LukeCepza/SomaStim/Others/Matlab/Sos2.png

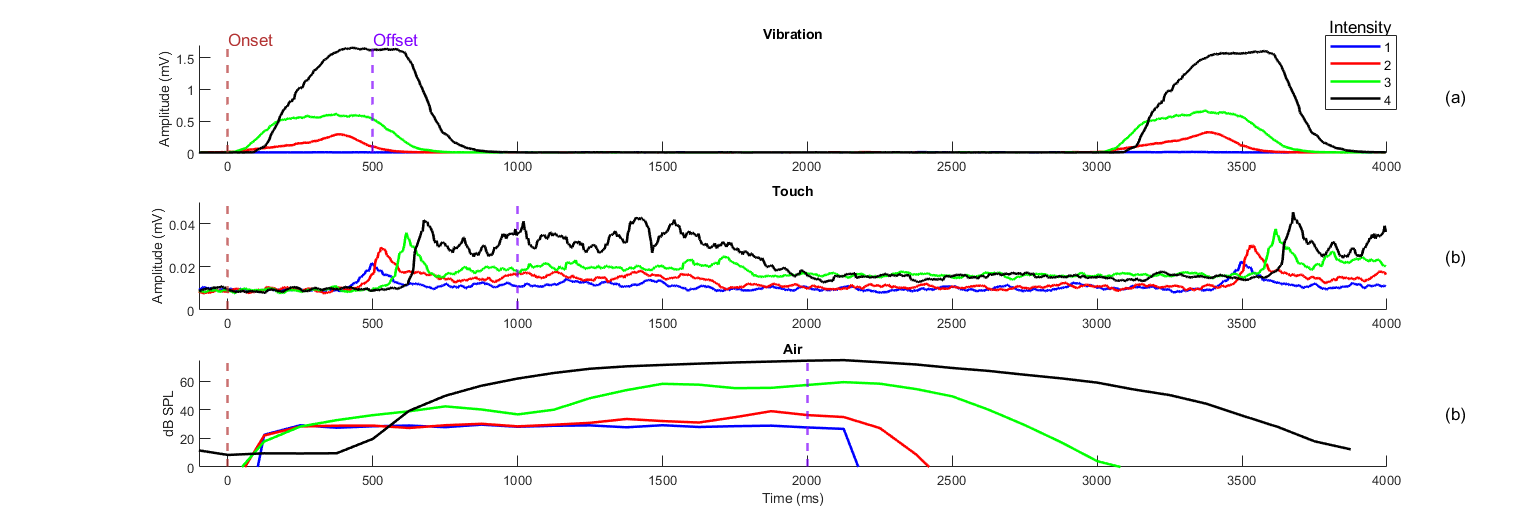
Others/Matlab/Sos2.png
