LukeCepza/SomaStim/Design/CaressModule_NeuroSense_SLDPRT_STL/CaricasFull - T_MD_LoadCell-1.STL

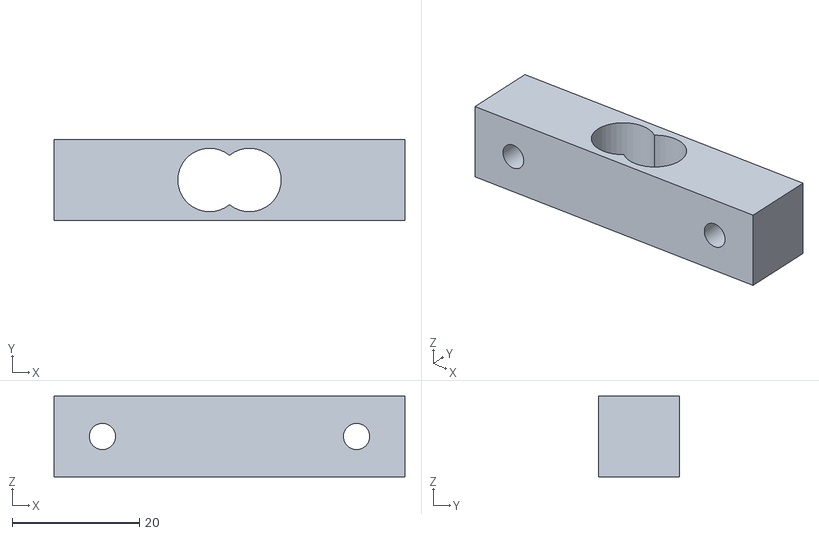
[picture p16: CAD file, 2023-08-07]
Design/CaressModule_NeuroSense_SLDPRT_STL/CaricasFull - T_MD_LoadCell-1.STL
55.2 x 12.7 x 12.7
