LukeCepza/SomaStim/Design/CaressModule_NeuroSense_SLDPRT_STL/CaricasFull - T_MD_RollerAxis-1.STL

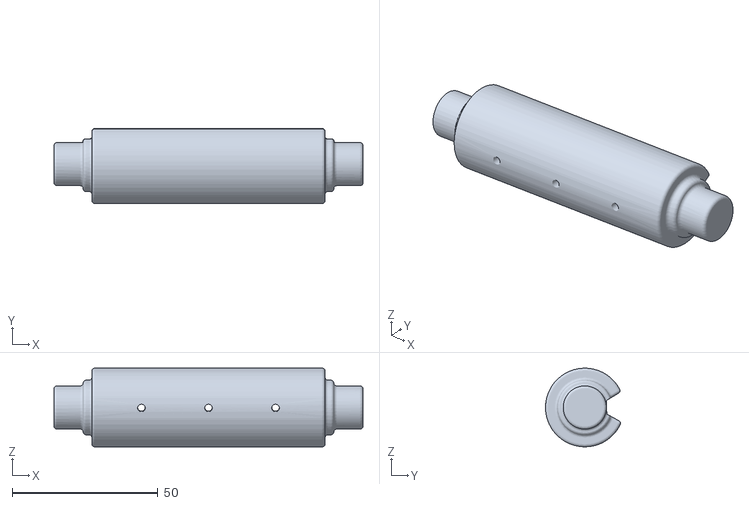
[picture p17: CAD file, 2023-08-07]
Design/CaressModule_NeuroSense_SLDPRT_STL/CaricasFull - T_MD_RollerAxis-1.STL
106.0 x 25.7 x 27.0
