LukeCepza/SomaStim/Design/CaressModule_NeuroSense_SLDPRT_STL/CaricasFull - T_MD_MotorSupport-1.STL

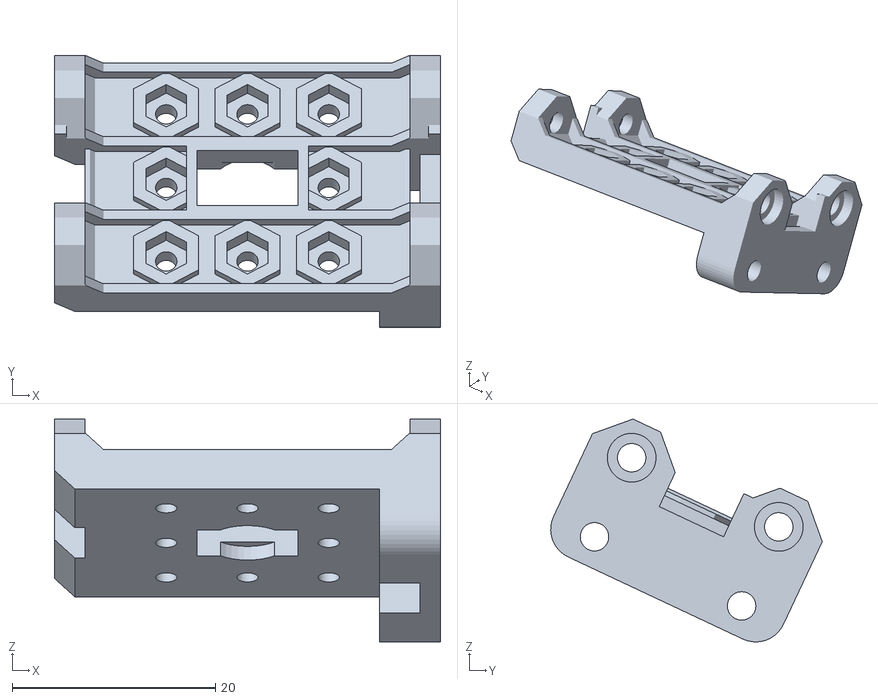
[picture p18: CAD file, 2023-08-07]
Design/CaressModule_NeuroSense_SLDPRT_STL/CaricasFull - T_MD_MotorSupport-1.STL
38.0 x 26.7 x 21.9
