LukeCepza/SomaStim/Design/CaressModule_NeuroSense_SLDPRT_STL/CaricasFull - T_MD_LateralBehind-1.STL

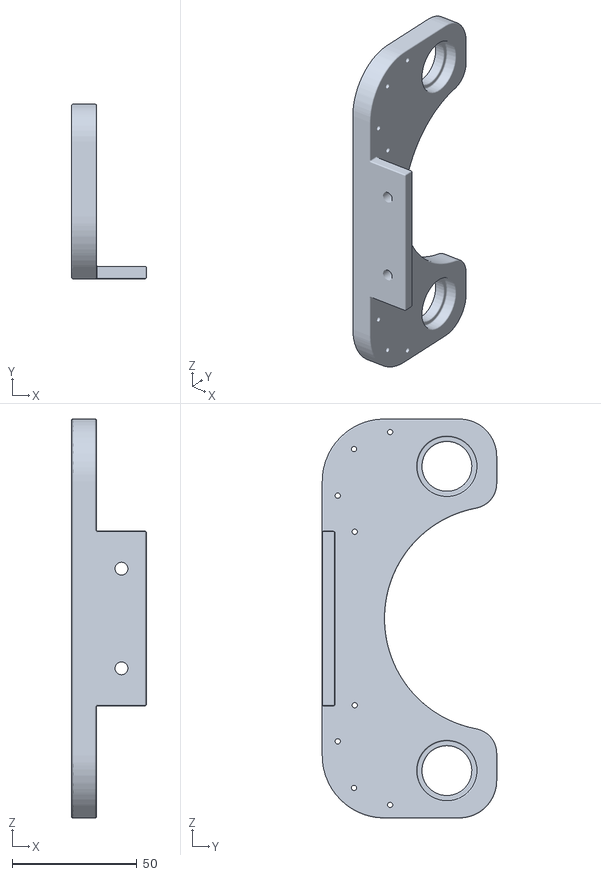
[picture p19: CAD file, 2023-08-07]
Design/CaressModule_NeuroSense_SLDPRT_STL/CaricasFull - T_MD_LateralBehind-1.STL
30.0 x 70.0 x 160.0
