LukeCepza/SomaStim/Design/CaressModule_NeuroSense_SLDPRT_STL/CaricasFull.SLDASM

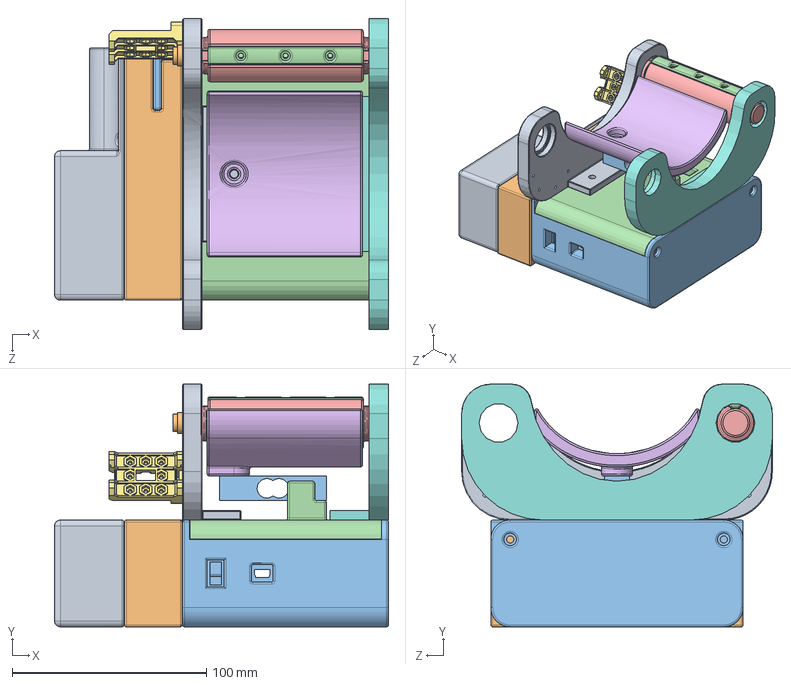
[picture p20: CAD file, 2023-08-07]
Design/CaressModule_NeuroSense_SLDPRT_STL/CaricasFull.SLDASM
172.0 x 125.0 x 160.0 mm
T_MD_CouplingMotor
T_MD_LateralBehind
T_MD_LateralFront
T_MD_LoadCell
T_MD_MotorSupport
T_MD_Plate
T_MD_RollerAxis
T_MD_RollerBar
T_MD_LoadCellBase
T_MD_BaseElectroV2
T_MD_BatteryPack
T_MD_BatteryPackLid
T_MD_18650
