LukeCepza/SomaStim/Design/CaressModule_NeuroSense_SLDPRT_STL/CaricasFull - T_MD_LoadCellBase-1.STL

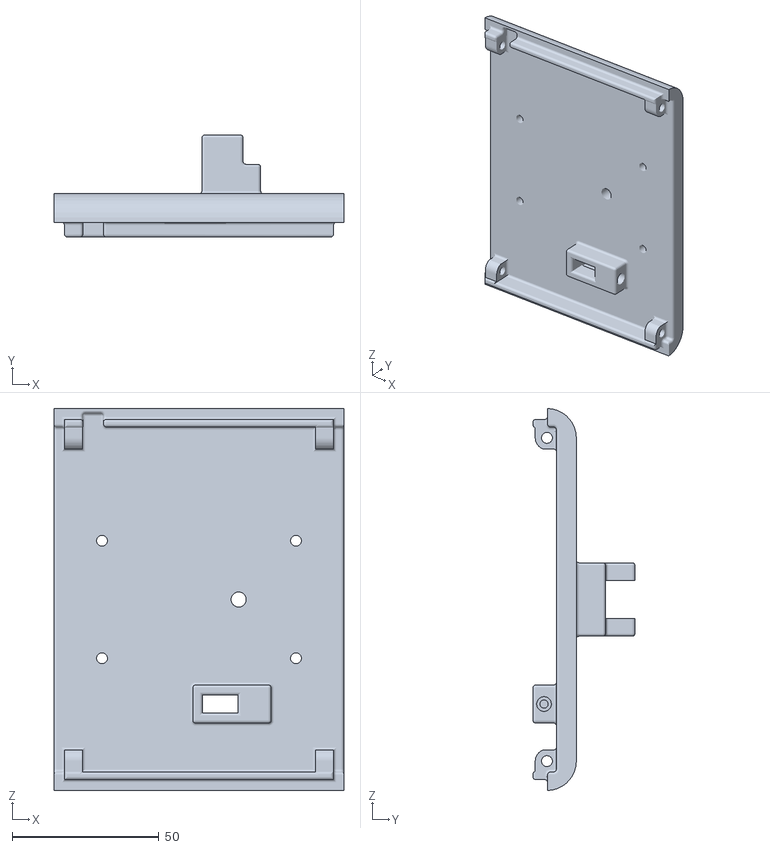
[picture p21: CAD file, 2023-08-07]
Design/CaressModule_NeuroSense_SLDPRT_STL/CaricasFull - T_MD_LoadCellBase-1.STL
98.6 x 34.8 x 130.0
