LukeCepza/SomaStim/Design/CaressModule_NeuroSense_SLDPRT_STL/CaricasFull - T_MD_BatteryPack-1.STL

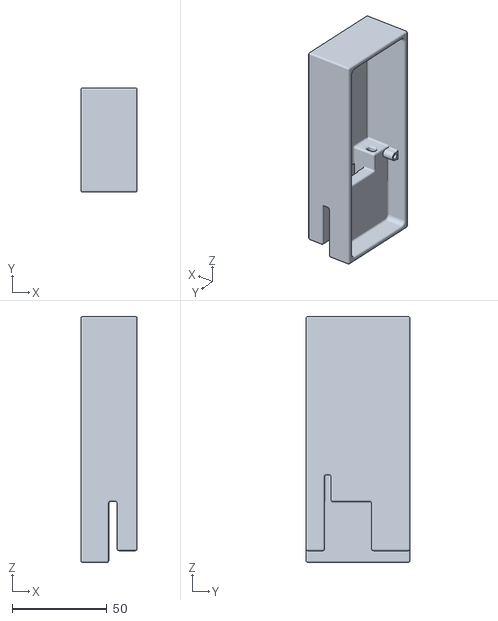
[picture p23: CAD file, 2023-08-07]
Design/CaressModule_NeuroSense_SLDPRT_STL/CaricasFull - T_MD_BatteryPack-1.STL
29.8 x 55.0 x 130.0
