LukeCepza/SomaStim/Design/MasterBox/files/lcd1602_box_and_stand.stl

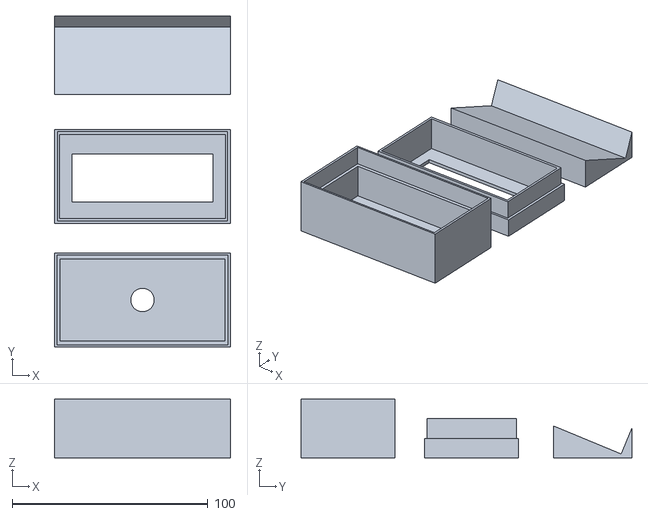
[picture p27: CAD file, 2023-08-01]
Design/MasterBox/files/lcd1602_box_and_stand.stl
90.0 x 169.0 x 30.0
