LukeCepza/SomaStim/Design/MasterBox/MasterBox1_base.STL

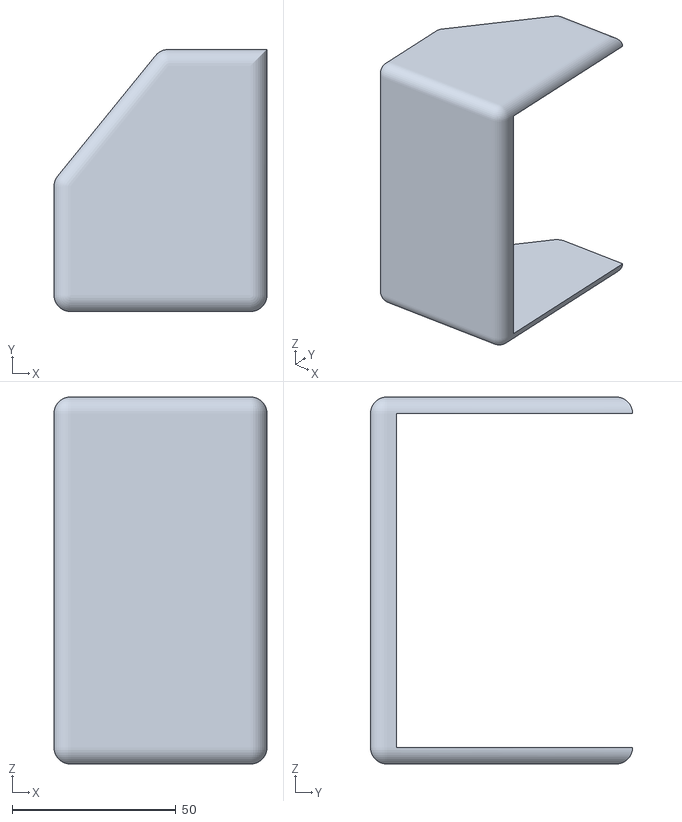
[picture p28: CAD file, 2023-08-01]
Design/MasterBox/MasterBox1_base.STL
65.0 x 80.0 x 112.0
