LukeCepza/SomaStim/Design/VibrationModule/VibrationDownwards_NeuroSense_SLDPRT_STL/V_Base.SLDPRT

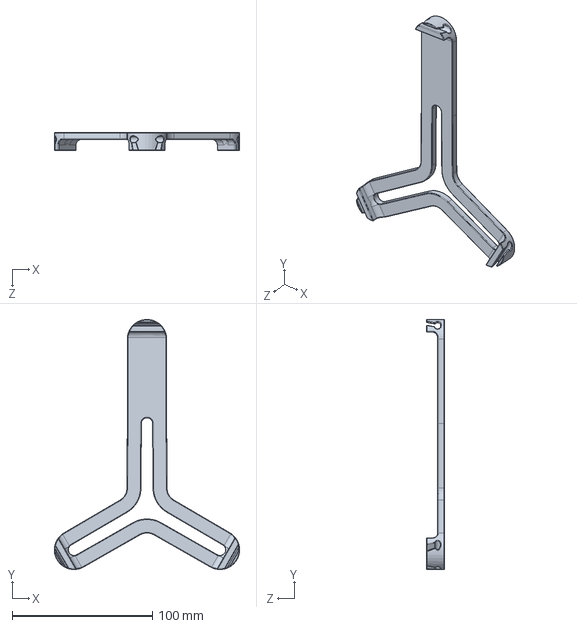
[picture p29: CAD file, 2023-08-01]
Design/VibrationModule/VibrationDownwards_NeuroSense_SLDPRT_STL/V_Base.SLDPRT
131.9 x 178.0 x 13.0 mm
