LukeCepza/SomaStim/PCB/Others/SEN-13879.step

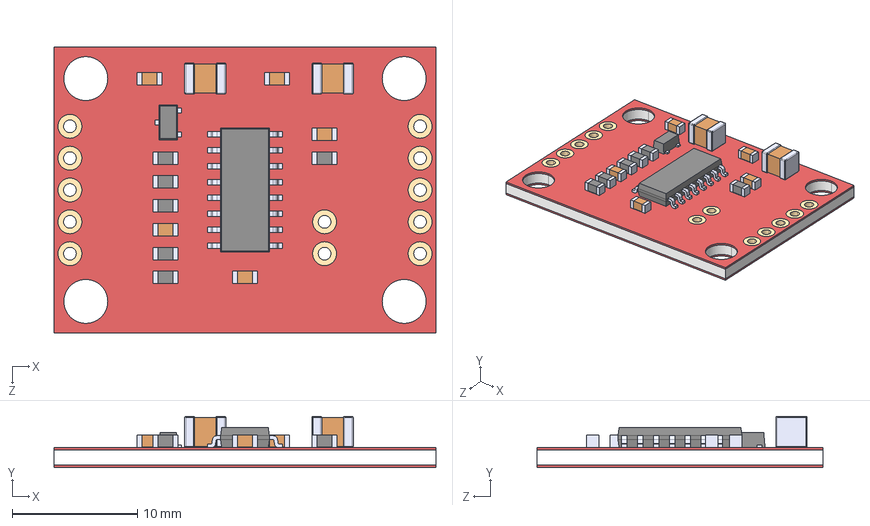
[picture p30: CAD file, 2023-08-07]
PCB/Others/SEN-13879.step
30.5 x 4.10 x 22.9 mm
