LukeCepza/SomaStim/Design/MasterBox/MasterBox1_LadoArduino.STL

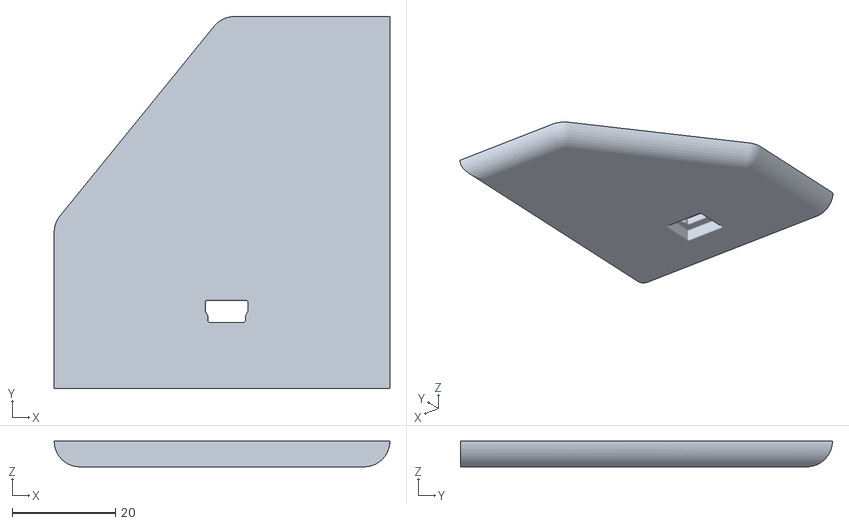
[picture p31: CAD file, 2023-08-01]
Design/MasterBox/MasterBox1_LadoArduino.STL
65.0 x 72.0 x 5.00
