LukeCepza/SomaStim/Design/VibrationModule/VibrationDownwards_NeuroSense_SLDPRT_STL/V_BaseSupport.SLDPRT

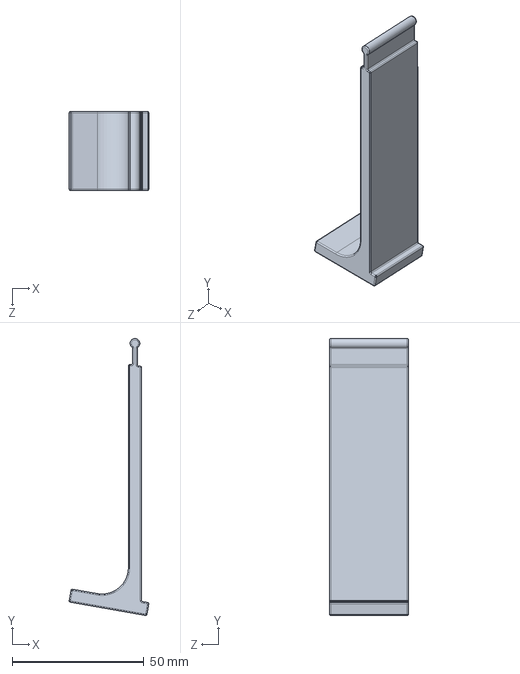
[picture p32: CAD file, 2023-08-01]
Design/VibrationModule/VibrationDownwards_NeuroSense_SLDPRT_STL/V_BaseSupport.SLDPRT
30.3 x 105.1 x 30.0 mm
