LukeCepza/SomaStim/Design/MasterBox/MasterBox1_base2.STL

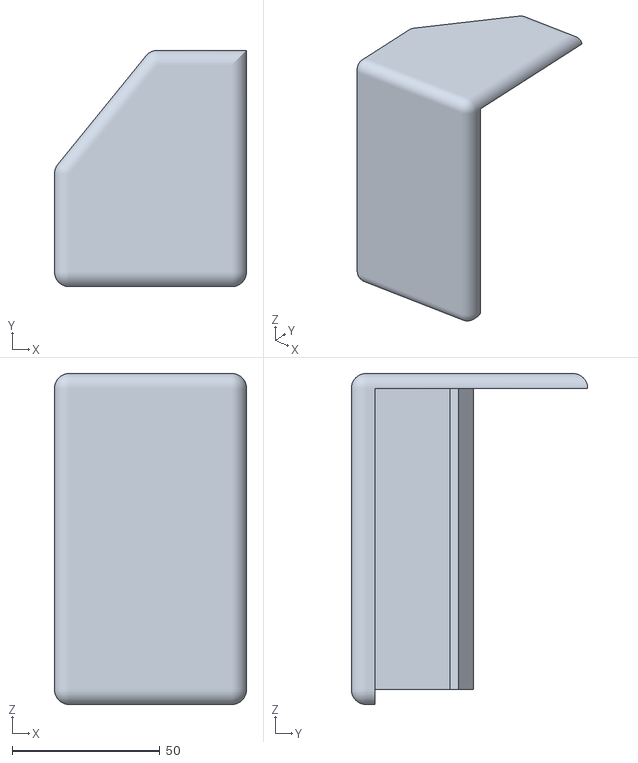
[picture p33: CAD file, 2023-08-01]
Design/MasterBox/MasterBox1_base2.STL
65.0 x 80.0 x 112.0
