LukeCepza/SomaStim/Design/VibrationModule/VibrationDownwards_NeuroSense_SLDPRT_STL/VibrationModule - V_BaseSupport-2.STL

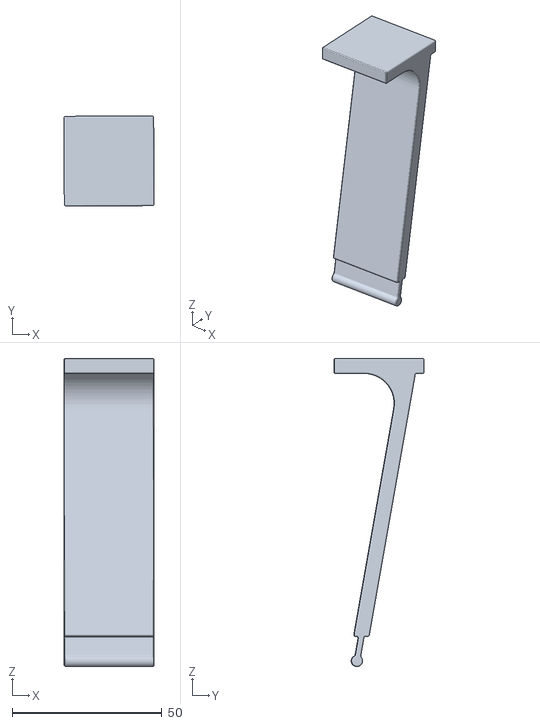
[picture p34: CAD file, 2023-08-01]
Design/VibrationModule/VibrationDownwards_NeuroSense_SLDPRT_STL/VibrationModule - V_BaseSupport-2.STL
30.2 x 30.2 x 102.8
