LukeCepza/SomaStim/Design/VibrationModule/VibrationUpwards_NeuroSense_SLDPRT_STL/Lower.SLDPRT

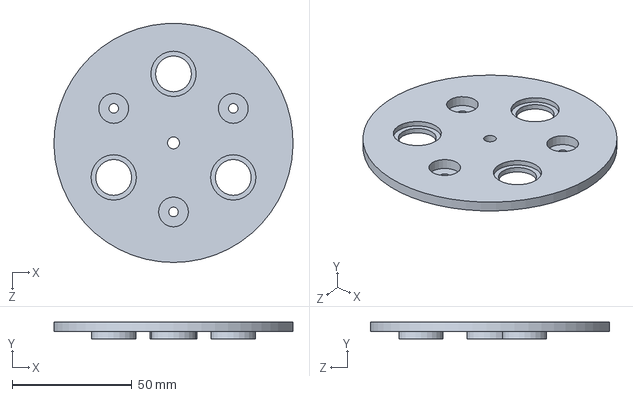
[picture p35: CAD file, 2023-08-07]
Design/VibrationModule/VibrationUpwards_NeuroSense_SLDPRT_STL/Lower.SLDPRT
100.0 x 7.00 x 99.9 mm
