LukeCepza/SomaStim/Design/MasterBox/MasterBox1_pantalto.STL

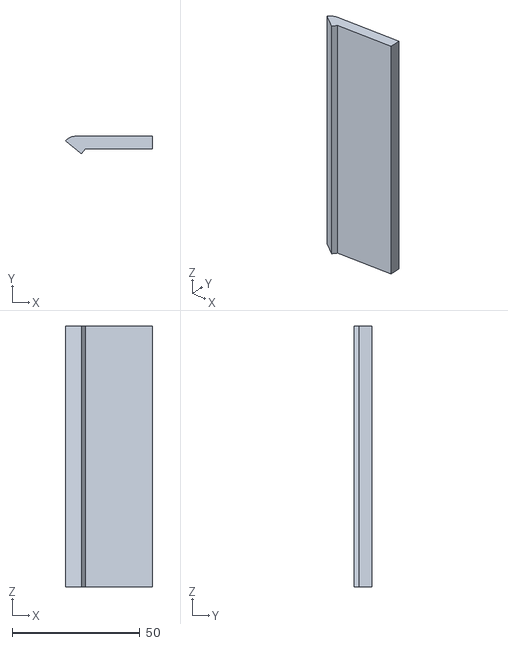
[picture p36: CAD file, 2023-08-01]
Design/MasterBox/MasterBox1_pantalto.STL
34.0 x 6.89 x 102.0
