LukeCepza/SomaStim/Design/MasterBox/MasterBox1.SLDPRT

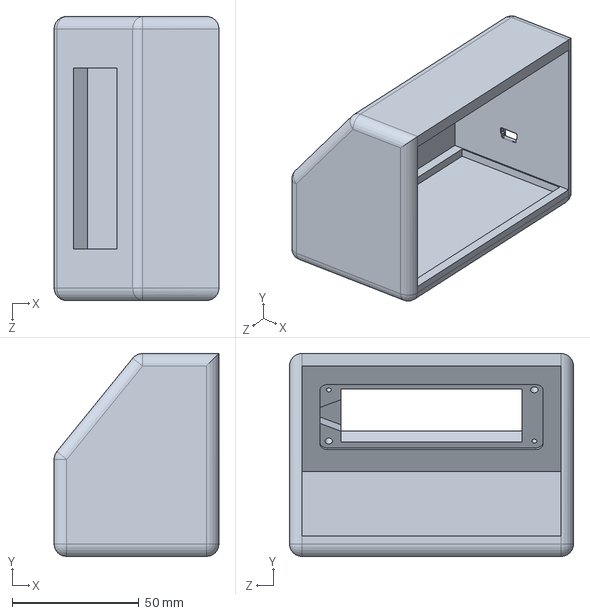
[picture p37: CAD file, 2023-08-01]
Design/MasterBox/MasterBox1.SLDPRT
65.0 x 80.0 x 112.0 mm
