LukeCepza/SomaStim/Design/VibrationModule/VibrationDownwards_NeuroSense_SLDPRT_STL/VibrationModule - V_MotorHolder-1.STL

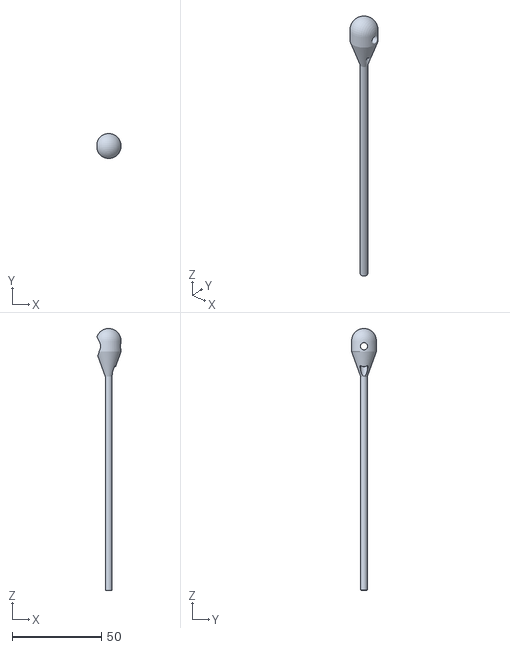
[picture p38: CAD file, 2023-08-01]
Design/VibrationModule/VibrationDownwards_NeuroSense_SLDPRT_STL/VibrationModule - V_MotorHolder-1.STL
13.6 x 14.0 x 147.0
