LukeCepza/SomaStim/Design/AirModule_NeuroSense_SLDPRT_STL/AirModule - Pipe-1.STL

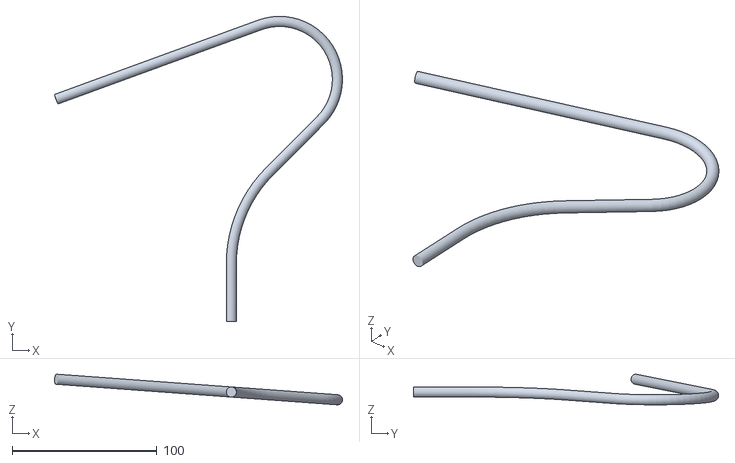
[picture p39: CAD file, 2023-08-01]
Design/AirModule_NeuroSense_SLDPRT_STL/AirModule - Pipe-1.STL
198.8 x 210.8 x 21.2
