LukeCepza/SomaStim/Design/MasterBox/MasterBox1_pantalla.STL

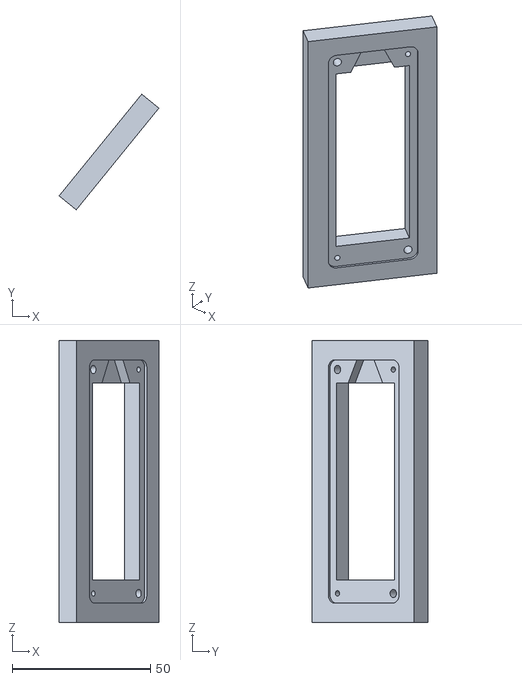
[picture p40: CAD file, 2023-08-01]
Design/MasterBox/MasterBox1_pantalla.STL
36.1 x 41.8 x 102.0
