LukeCepza/SomaStim/Design/VibrationModule/VibrationDownwards_NeuroSense_SLDPRT_STL/VibrationModule - V_BaseSupport-1.STL

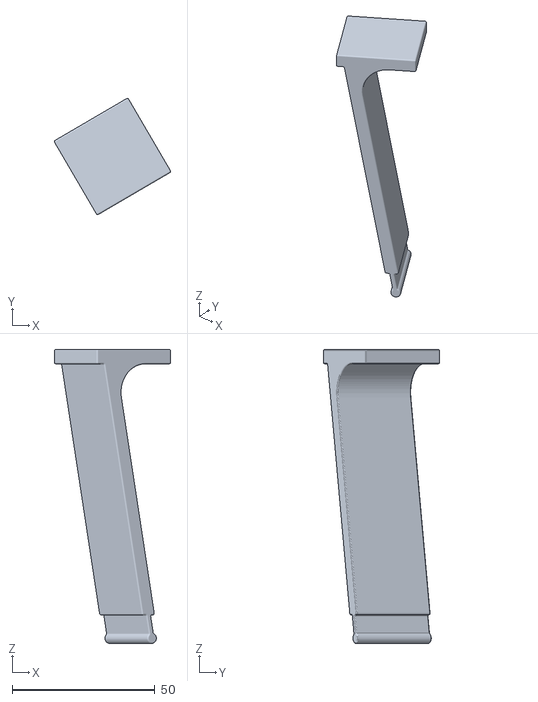
[picture p41: CAD file, 2023-08-01]
Design/VibrationModule/VibrationDownwards_NeuroSense_SLDPRT_STL/VibrationModule - V_BaseSupport-1.STL
40.7 x 40.7 x 102.8
