LukeCepza/SomaStim/Design/AirModule_NeuroSense_SLDPRT_STL/AirModule - 18650-1.STL

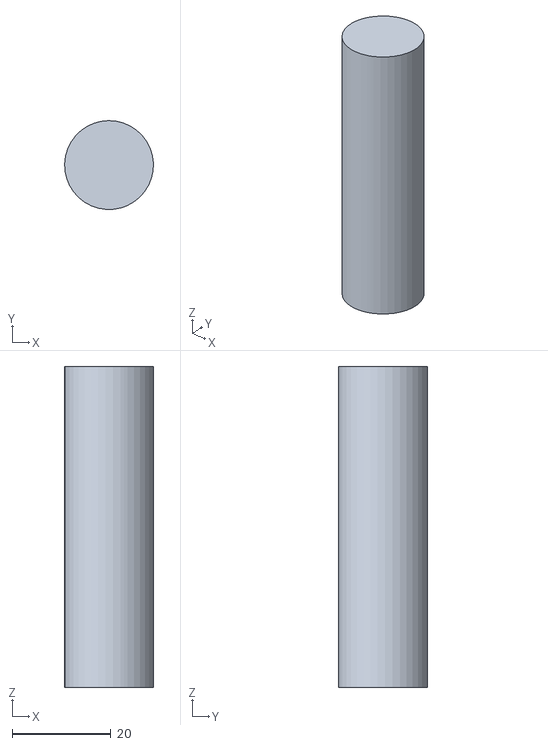
[picture p42: CAD file, 2023-08-01]
Design/AirModule_NeuroSense_SLDPRT_STL/AirModule - 18650-1.STL
18.0 x 18.0 x 65.0
