LukeCepza/SomaStim/Design/CaressModule_NeuroSense_SLDPRT_STL/T_MD_BaseElectro.SLDPRT

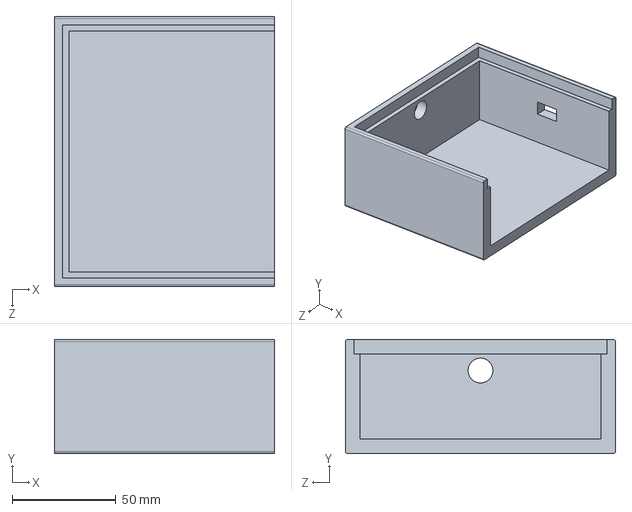
[picture p43: CAD file, 2023-08-07]
Design/CaressModule_NeuroSense_SLDPRT_STL/T_MD_BaseElectro.SLDPRT
106.0 x 55.0 x 130.0 mm
