LukeCepza/SomaStim/Design/MasterBox/MasterBox1_pantbajo.STL

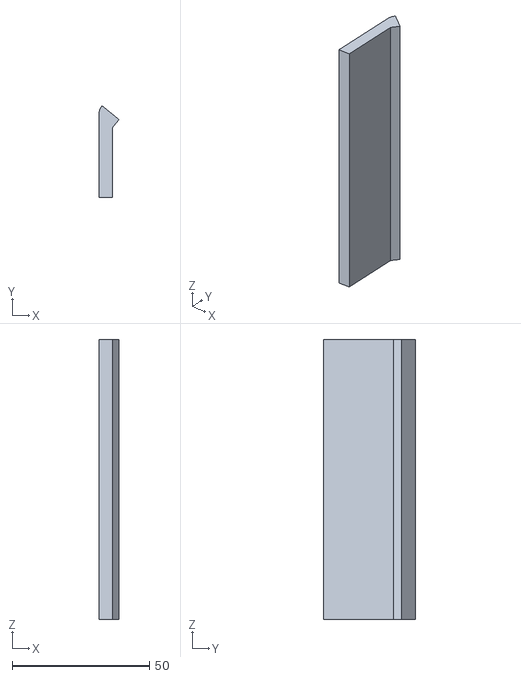
[picture p44: CAD file, 2023-08-01]
Design/MasterBox/MasterBox1_pantbajo.STL
7.33 x 33.4 x 102.0
