LukeCepza/SomaStim/Design/AirModule_NeuroSense_SLDPRT_STL/Pipe.SLDPRT

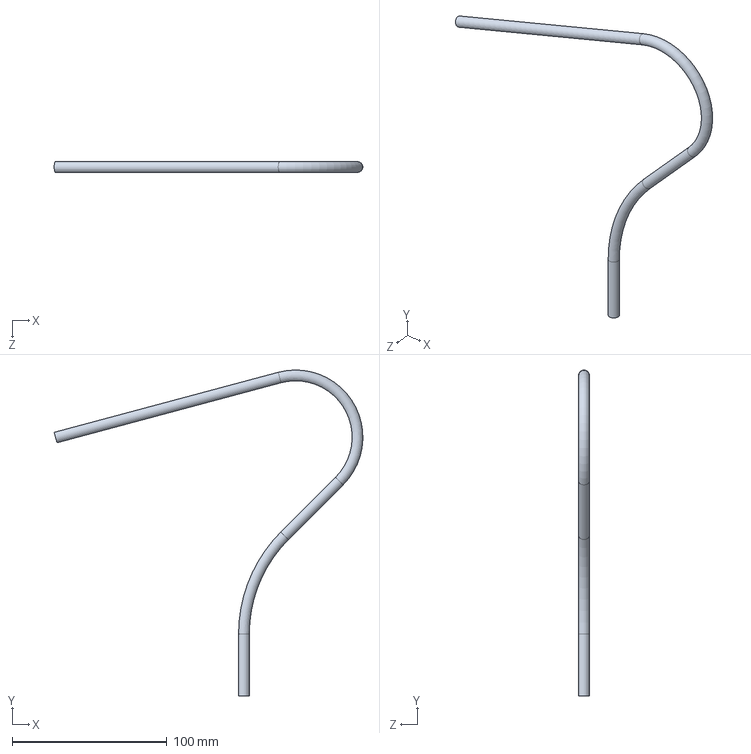
[picture p45: CAD file, 2023-08-01]
Design/AirModule_NeuroSense_SLDPRT_STL/Pipe.SLDPRT
199.6 x 210.8 x 7.00 mm
