LukeCepza/SomaStim/Design/AirModule_NeuroSense_SLDPRT_STL/A_FanBoxTilted.SLDPRT

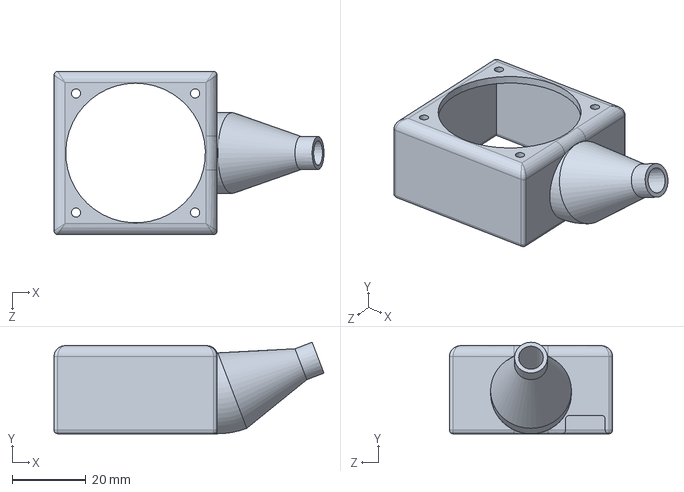
[picture p46: CAD file, 2023-08-01]
Design/AirModule_NeuroSense_SLDPRT_STL/A_FanBoxTilted.SLDPRT
73.5 x 24.9 x 44.4 mm
