LukeCepza/SomaStim/Design/AirModule_NeuroSense_SLDPRT_STL/AirModule - A_ElectroBoxLid-1.STL

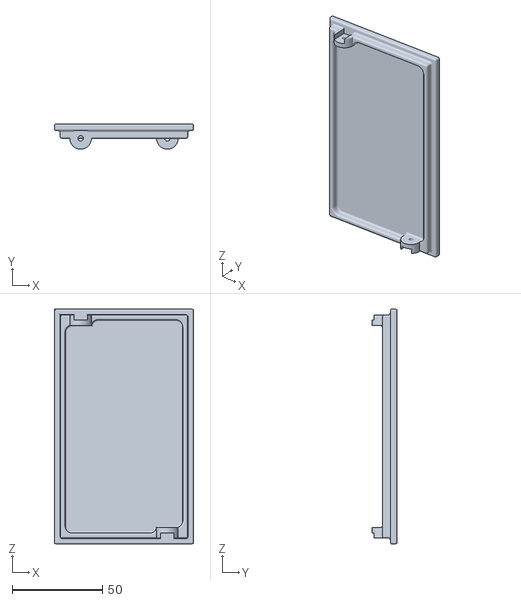
[picture p47: CAD file, 2023-08-01]
Design/AirModule_NeuroSense_SLDPRT_STL/AirModule - A_ElectroBoxLid-1.STL
77.0 x 14.0 x 130.0
