LukeCepza/SomaStim/Design/AirModule_NeuroSense_SLDPRT_STL/AirModule - A_ElectroBox-1.STL

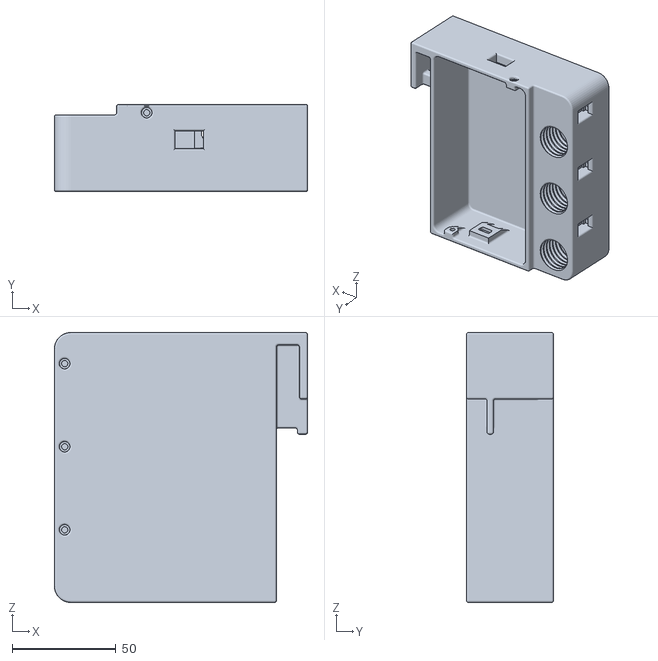
[picture p48: CAD file, 2023-08-01]
Design/AirModule_NeuroSense_SLDPRT_STL/AirModule - A_ElectroBox-1.STL
122.0 x 42.0 x 130.0
