LukeCepza/SomaStim/Design/AirModule_NeuroSense_SLDPRT_STL/AirModule - A_FanBoxTilted-1.STL

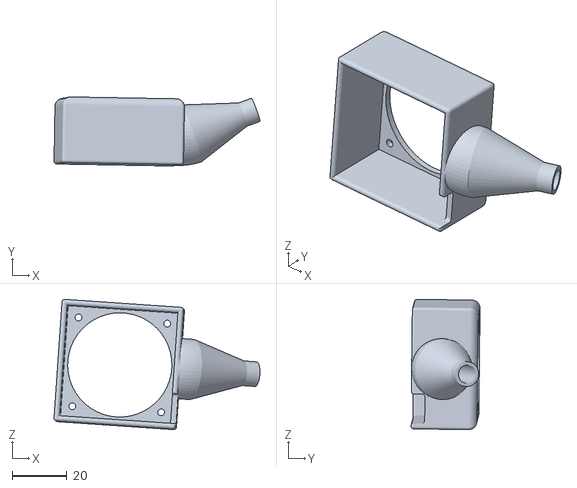
[picture p49: CAD file, 2023-08-01]
Design/AirModule_NeuroSense_SLDPRT_STL/AirModule - A_FanBoxTilted-1.STL
75.0 x 25.2 x 47.5
