LukeCepza/SomaStim/Design/CaressModule_NeuroSense_SLDPRT_STL/T_MD_MotorSupport.SLDPRT

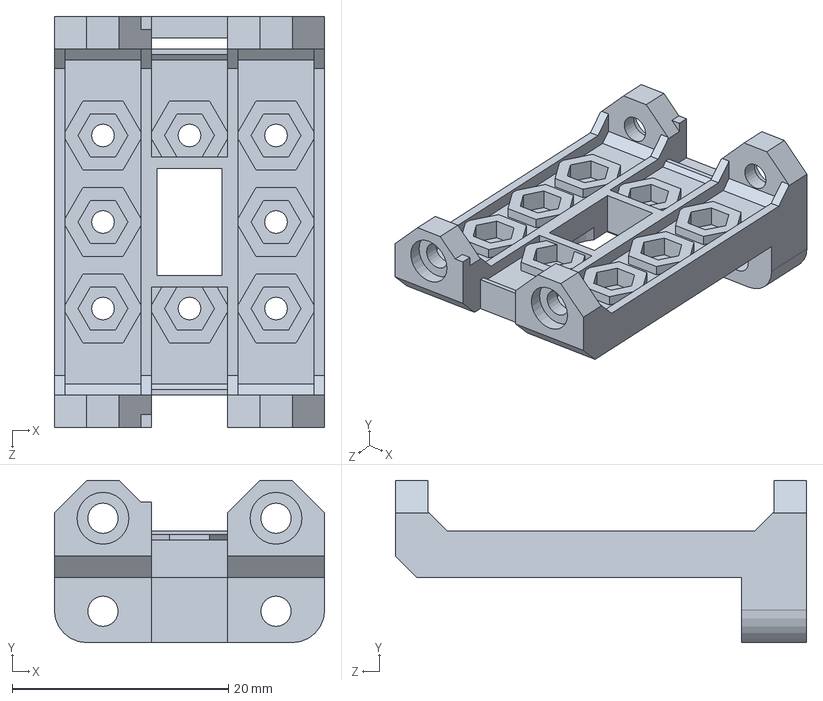
[picture p50: CAD file, 2023-08-07]
Design/CaressModule_NeuroSense_SLDPRT_STL/T_MD_MotorSupport.SLDPRT
25.0 x 15.0 x 38.0 mm
