LukeCepza/SomaStim/Design/CaressModule_NeuroSense_SLDPRT_STL/T_MD_Base.SLDPRT

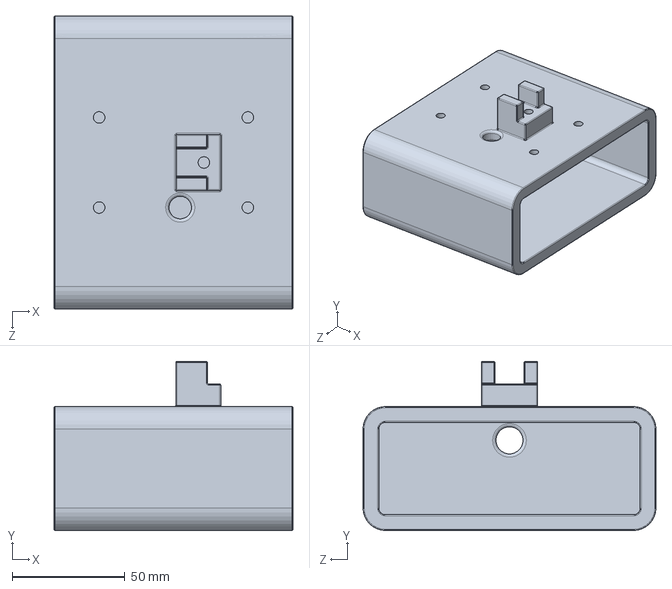
[picture p51: CAD file, 2023-08-07]
Design/CaressModule_NeuroSense_SLDPRT_STL/T_MD_Base.SLDPRT
106.0 x 75.0 x 130.0 mm
